arneman44/Modular-Lab-PowerSupply/Docs/page_1.png

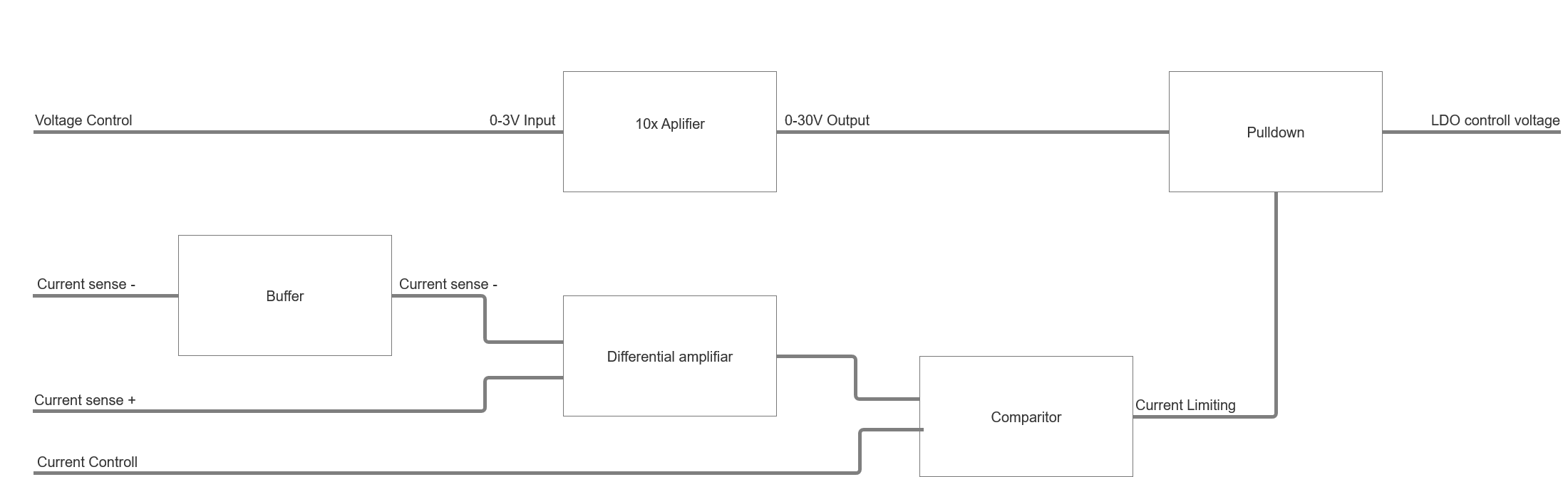
Docs/page_1.png
