arneman44/Modular-Lab-PowerSupply/Docs/power_module.png

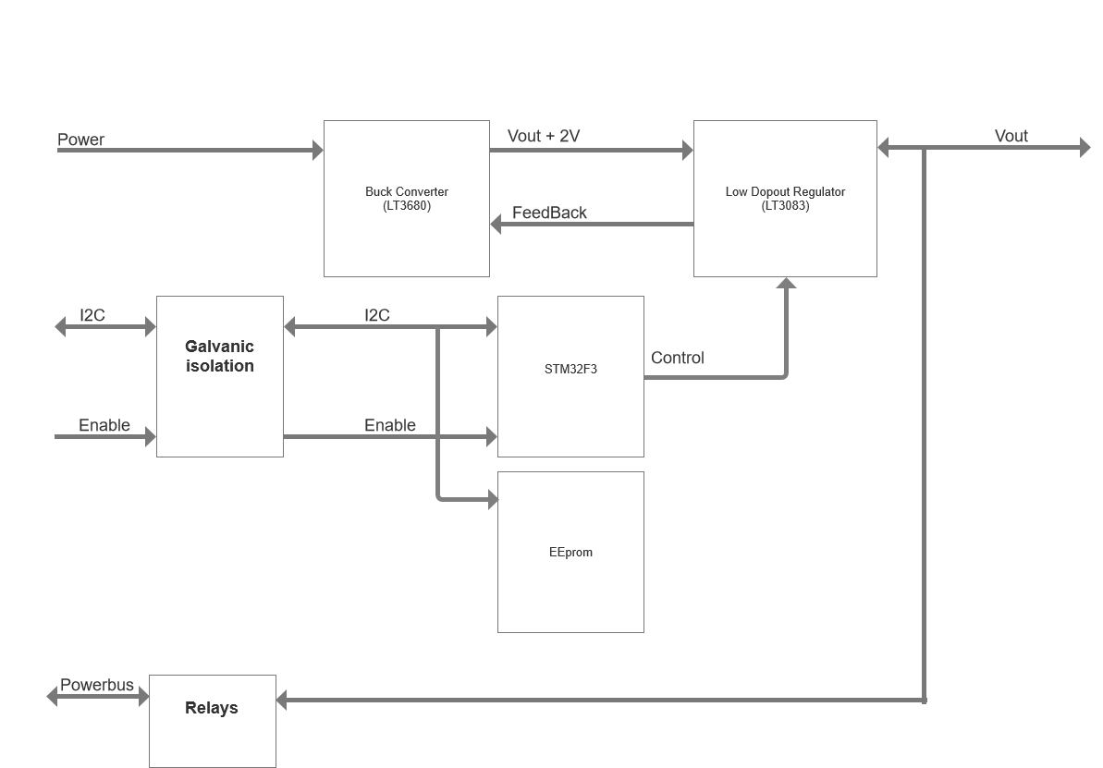
Docs/power_module.png
