arneman44/Modular-Lab-PowerSupply/LCDboard/LCDboard/STM32_LCD/LCD.kicad_sch

## KiCad design LCDboard/LCDboard/STM32_LCD/LCD.kicad_sch (2021-03-07)

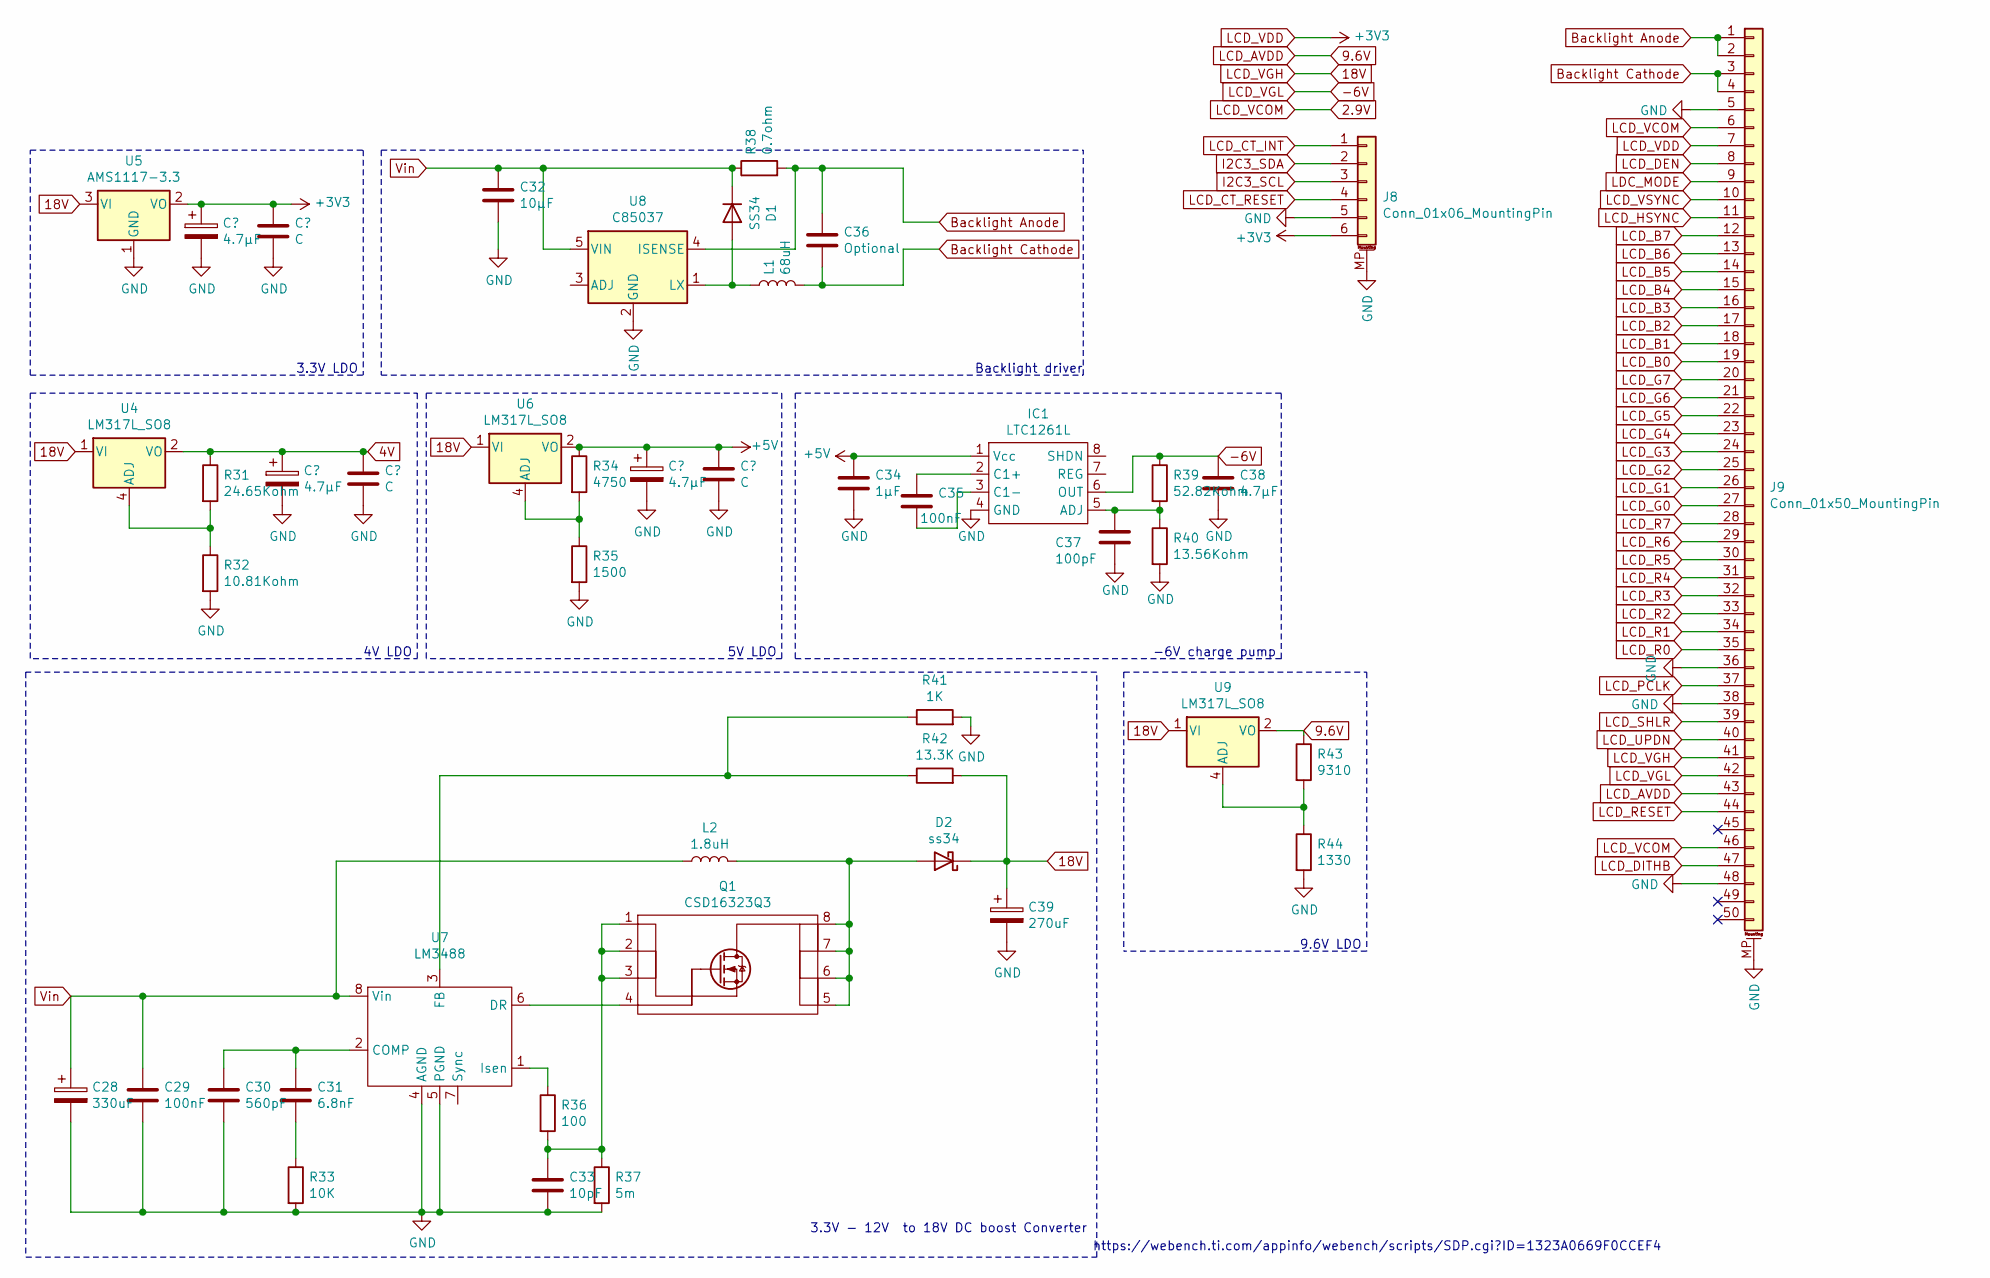
[picture p26: schematic LCD.kicad_sch]

Parts:
C28: 330uF
C29, C35: 100nF
C30: 560pF
C31: 6.8nF
C32: 10µF; C_1206_3216Metric_Pad1.42x1.75mm_HandSolder
C33: 10pF
C34: 1µF
C36: Optional; C_0805_2012Metric_Pad1.15x1.40mm_HandSolder
C37: 100pF
C38: 4.7µF
C39: 270uF
D1: SS34; D_SMA_Handsoldering
D2: ss34
IC1: LTC1261L
J8: Conn_01x06_MountingPin
J9: Conn_01x50_MountingPin
L1: 68uH; L_Bourns-SRN8040_8x8.15mm; Partnr SMNR8040-680MT; LCSC C266439
L2: 1.8uH
Q1: CSD16323Q3; TDSON-8-1
R31: 24.65Kohm
R32: 10.81Kohm
R33: 10K
R34: 4750
R35: 1500
R36: 100
R37: 5m
R38: 0.7ohm; R_1206_3216Metric_Pad1.42x1.75mm_HandSolder
R39: 52.82Kohm
R40: 13.56Kohm
R41: 1K
R42: 13.3K
R43: 9310
R44: 1330
U4, U6, U9: LM317L_SO8; SOIC-8_3.9x4.9mm_P1.27mm
U5: AMS1117-3.3; SOT-223-3_TabPin2
U7: LM3488
U8: C85037; SOT-89-5

Connections:
2.9V: J9.6, J9.46
4V: R31.1, U4.2 (VO), U4.3 (VO), U4.6 (VO), U4.7 (VO)
9.6V: J9.43, R43.1, U9.2 (VO), U9.3 (VO), U9.6 (VO), U9.7 (VO)
18V: C39.1, D2.1 (K), J9.41, R42.2, U4.1 (VI), U5.3 (VI), U6.1 (VI), U9.1 (VI)
+3V3: J8.6, J9.7, U5.2 (VO)
+5V: C34.1, IC1.1 (Vcc), R34.1, U6.2 (VO), U6.3 (VO), U6.6 (VO), U6.7 (VO)
-6V: C38.1, IC1.6 (OUT), J9.42, R39.1
Backlight Anode: C36.1, J9.1, J9.2, R38.2, U8.4 (ISENSE)
Backlight Cathode: C36.2, J9.3, J9.4, L1.2
GND: C28.2, C29.2, C30.2, C32.2, C33.2, C34.2, C37.2, C38.2, C39.2, IC1.4 (GND), J8.5, J8.MP (MountPin), J9.5, J9.36, J9.38, J9.48, J9.MP (MountPin), R32.2, R33.2, R35.2, R37.2, R40.2, R41.2, R44.2, U5.1 (GND), U7.4 (AGND), U7.5 (PGND), U8.2 (GND)
I2C3_SCL: J8.3
I2C3_SDA: J8.2
LCD_B0: J9.19
LCD_B1: J9.18
LCD_B2: J9.17
LCD_B3: J9.16
LCD_B4: J9.15
LCD_B5: J9.14
LCD_B6: J9.13
LCD_B7: J9.12
LCD_CT_INT: J8.1
LCD_CT_RESET: J8.4
LCD_DEN: J9.8
LCD_DITHB: J9.47
LCD_G0: J9.27
LCD_G1: J9.26
LCD_G2: J9.25
LCD_G3: J9.24
LCD_G4: J9.23
LCD_G5: J9.22
LCD_G6: J9.21
LCD_G7: J9.20
LCD_HSYNC: J9.11
LCD_PCLK: J9.37
LCD_R0: J9.35
LCD_R1: J9.34
LCD_R2: J9.33
LCD_R3: J9.32
LCD_R4: J9.31
LCD_R5: J9.30
LCD_R6: J9.29
LCD_R7: J9.28
LCD_RESET: J9.44
LCD_SHLR: J9.39
LCD_UPDN: J9.40
LCD_VSYNC: J9.10
LDC_MODE: J9.9
unnamed: C30.1, C31.1, U7.2 (COMP)
unnamed: C31.2, R33.1
unnamed: C33.1, Q1.1 (S), Q1.2 (S), Q1.3 (S), R36.2, R37.1
unnamed: C35.1, IC1.2 (C1+)
unnamed: C35.2, IC1.3 (C1-)
unnamed: C37.1, IC1.5 (ADJ), R39.2, R40.1
unnamed: D1.2 (A), L1.1, U8.1 (LX)
unnamed: D2.2 (A), L2.2, Q1.5 (D), Q1.6 (D), Q1.7 (D), Q1.8 (D)
unnamed: Q1.2 (S), Q1.3 (S)
unnamed: Q1.4 (G), U7.6 (DR)
unnamed: R31.2, R32.1, U4.4 (ADJ)
unnamed: R34.2, R35.1, U6.4 (ADJ)
unnamed: R36.1, U7.1 (Isen)
unnamed: R41.1, R42.1, U7.3 (FB)
unnamed: R43.2, R44.1, U9.4 (ADJ)
Vin: C28.1, C29.1, C32.1, D1.1 (K), L2.1, R38.1, U7.8 (Vin), U8.5 (VIN)

Notes on the sheet:
3.3V LDO
4V LDO
5V LDO
Backlight driver
3.3V - 12V to 18V DC boost Converter
https://webench.ti.com/appinfo/webench/scripts/SDP.cgi?ID=1323A0669F0CCEF4
-6V charge pump
9.6V LDO
