arneman44/Modular-Lab-PowerSupply/LCDboard/LCDboard/STM32_LCD/STM32_LCD.kicad_sch

## KiCad design LCDboard/LCDboard/STM32_LCD/STM32_LCD.kicad_sch (2021-03-07)

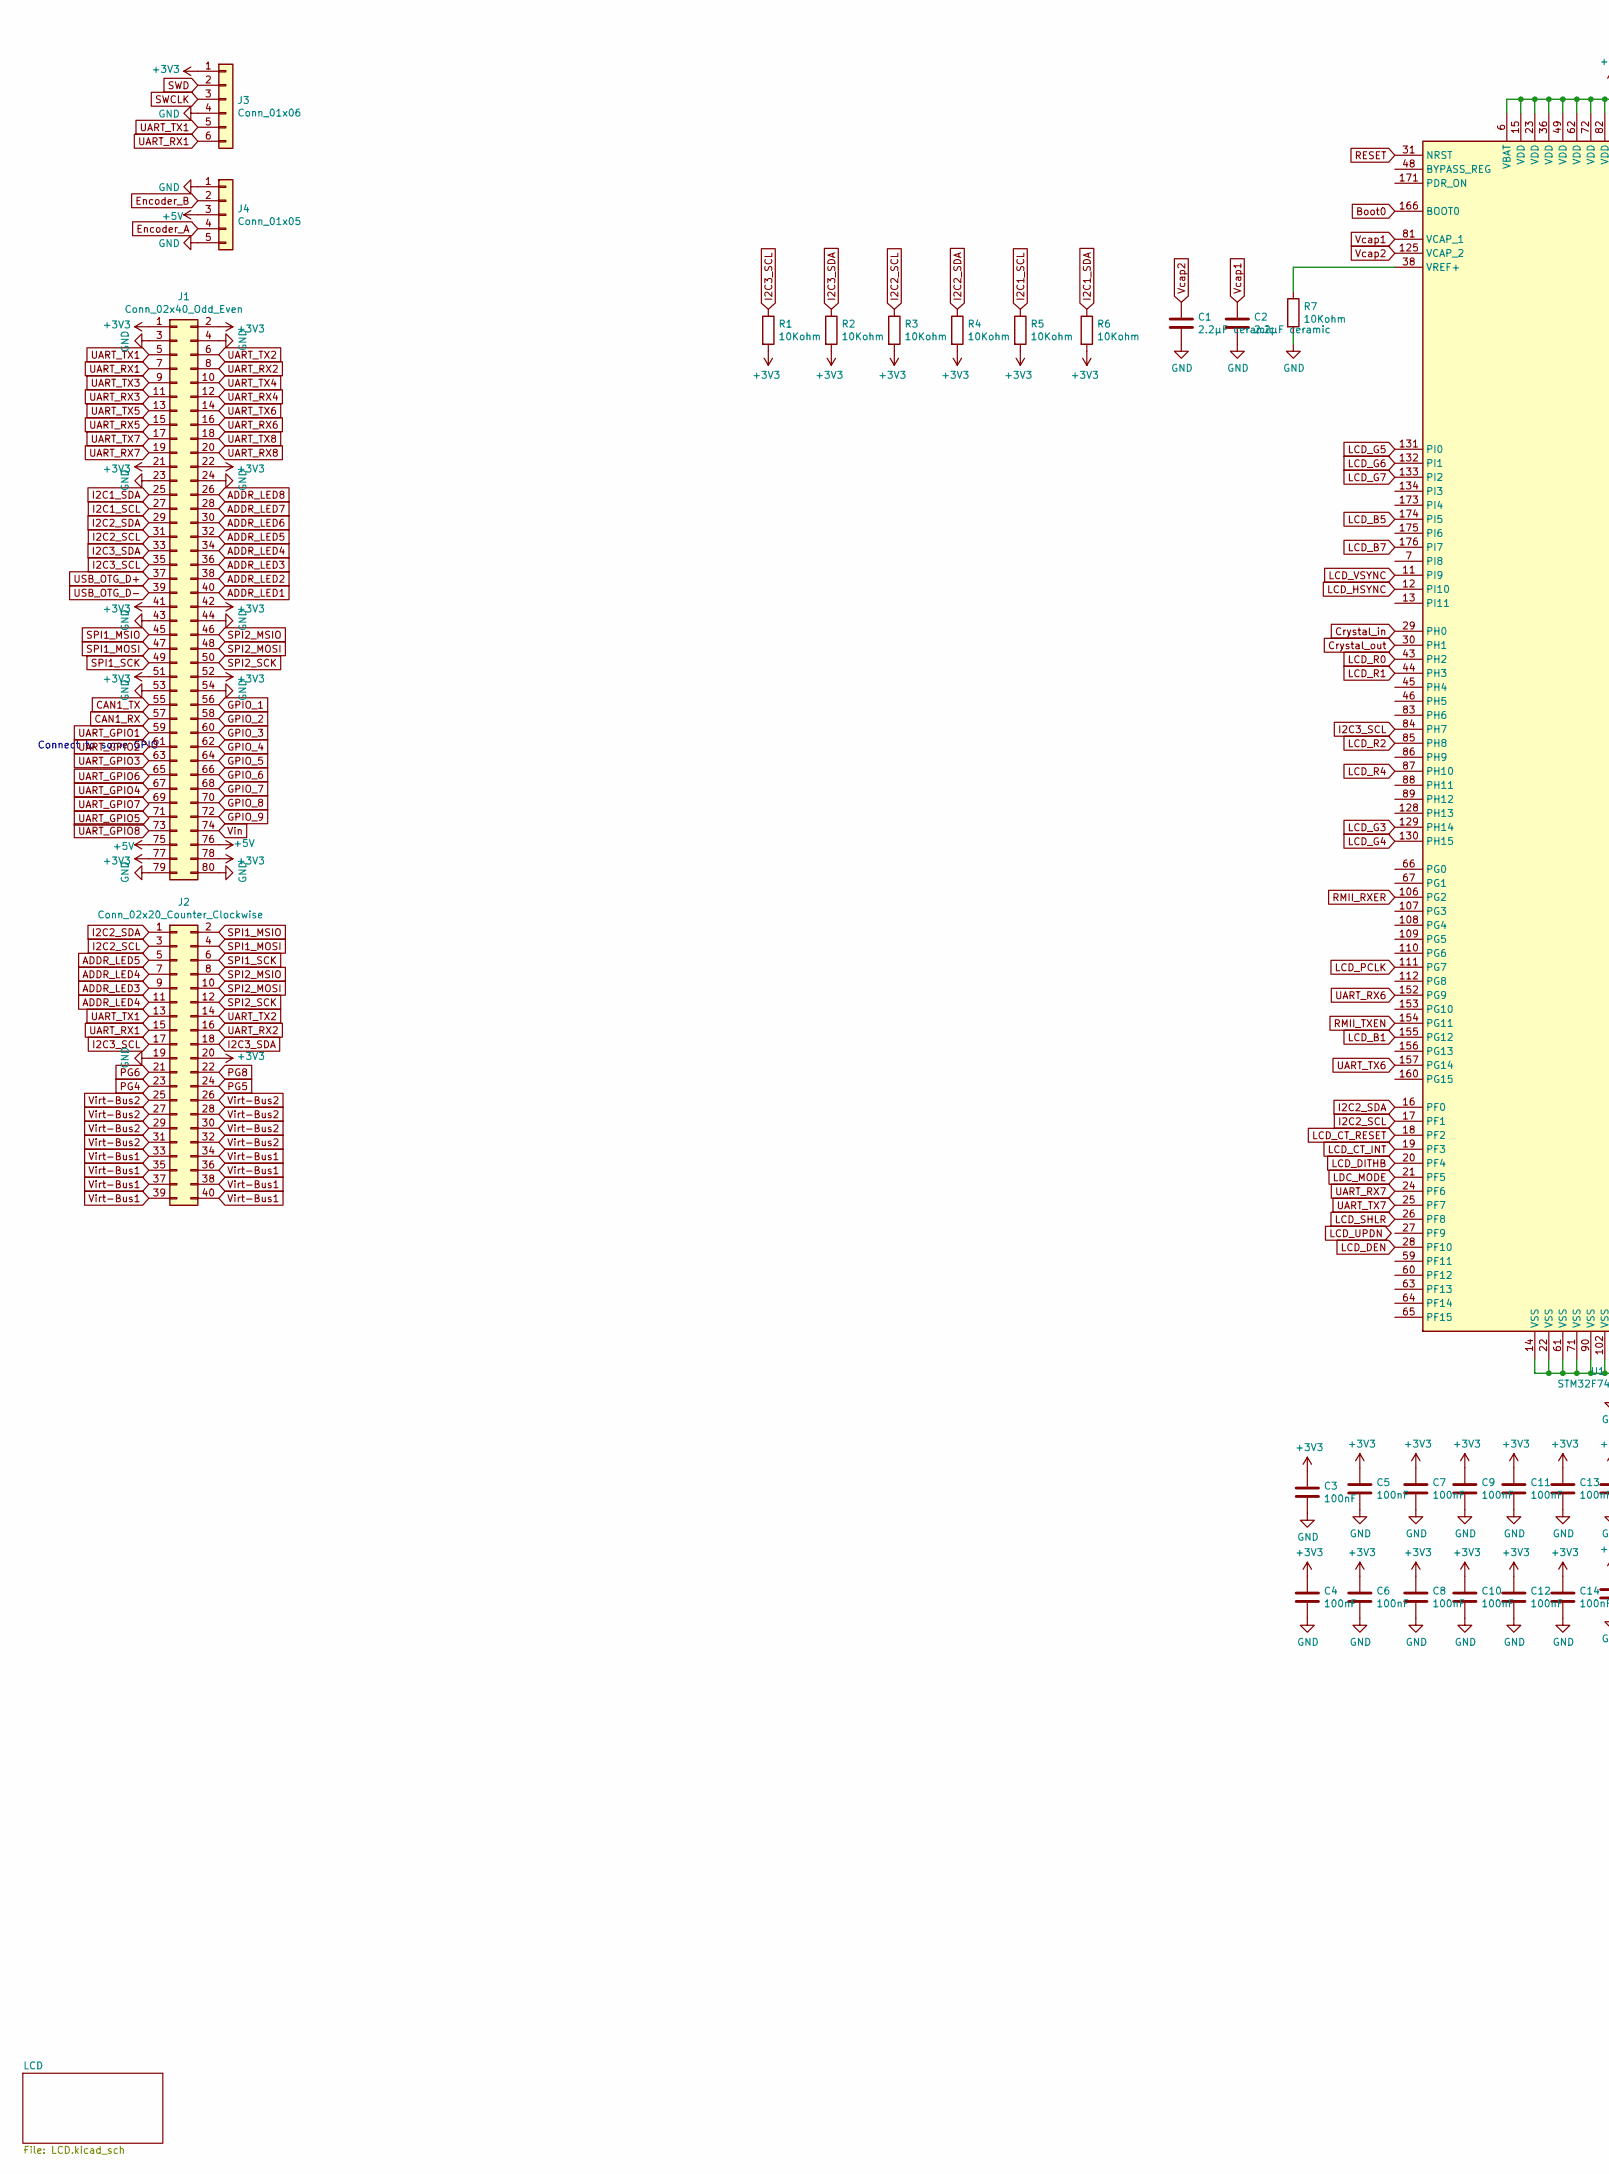
[picture p27: schematic STM32_LCD.kicad_sch, part in row 1, column 1]

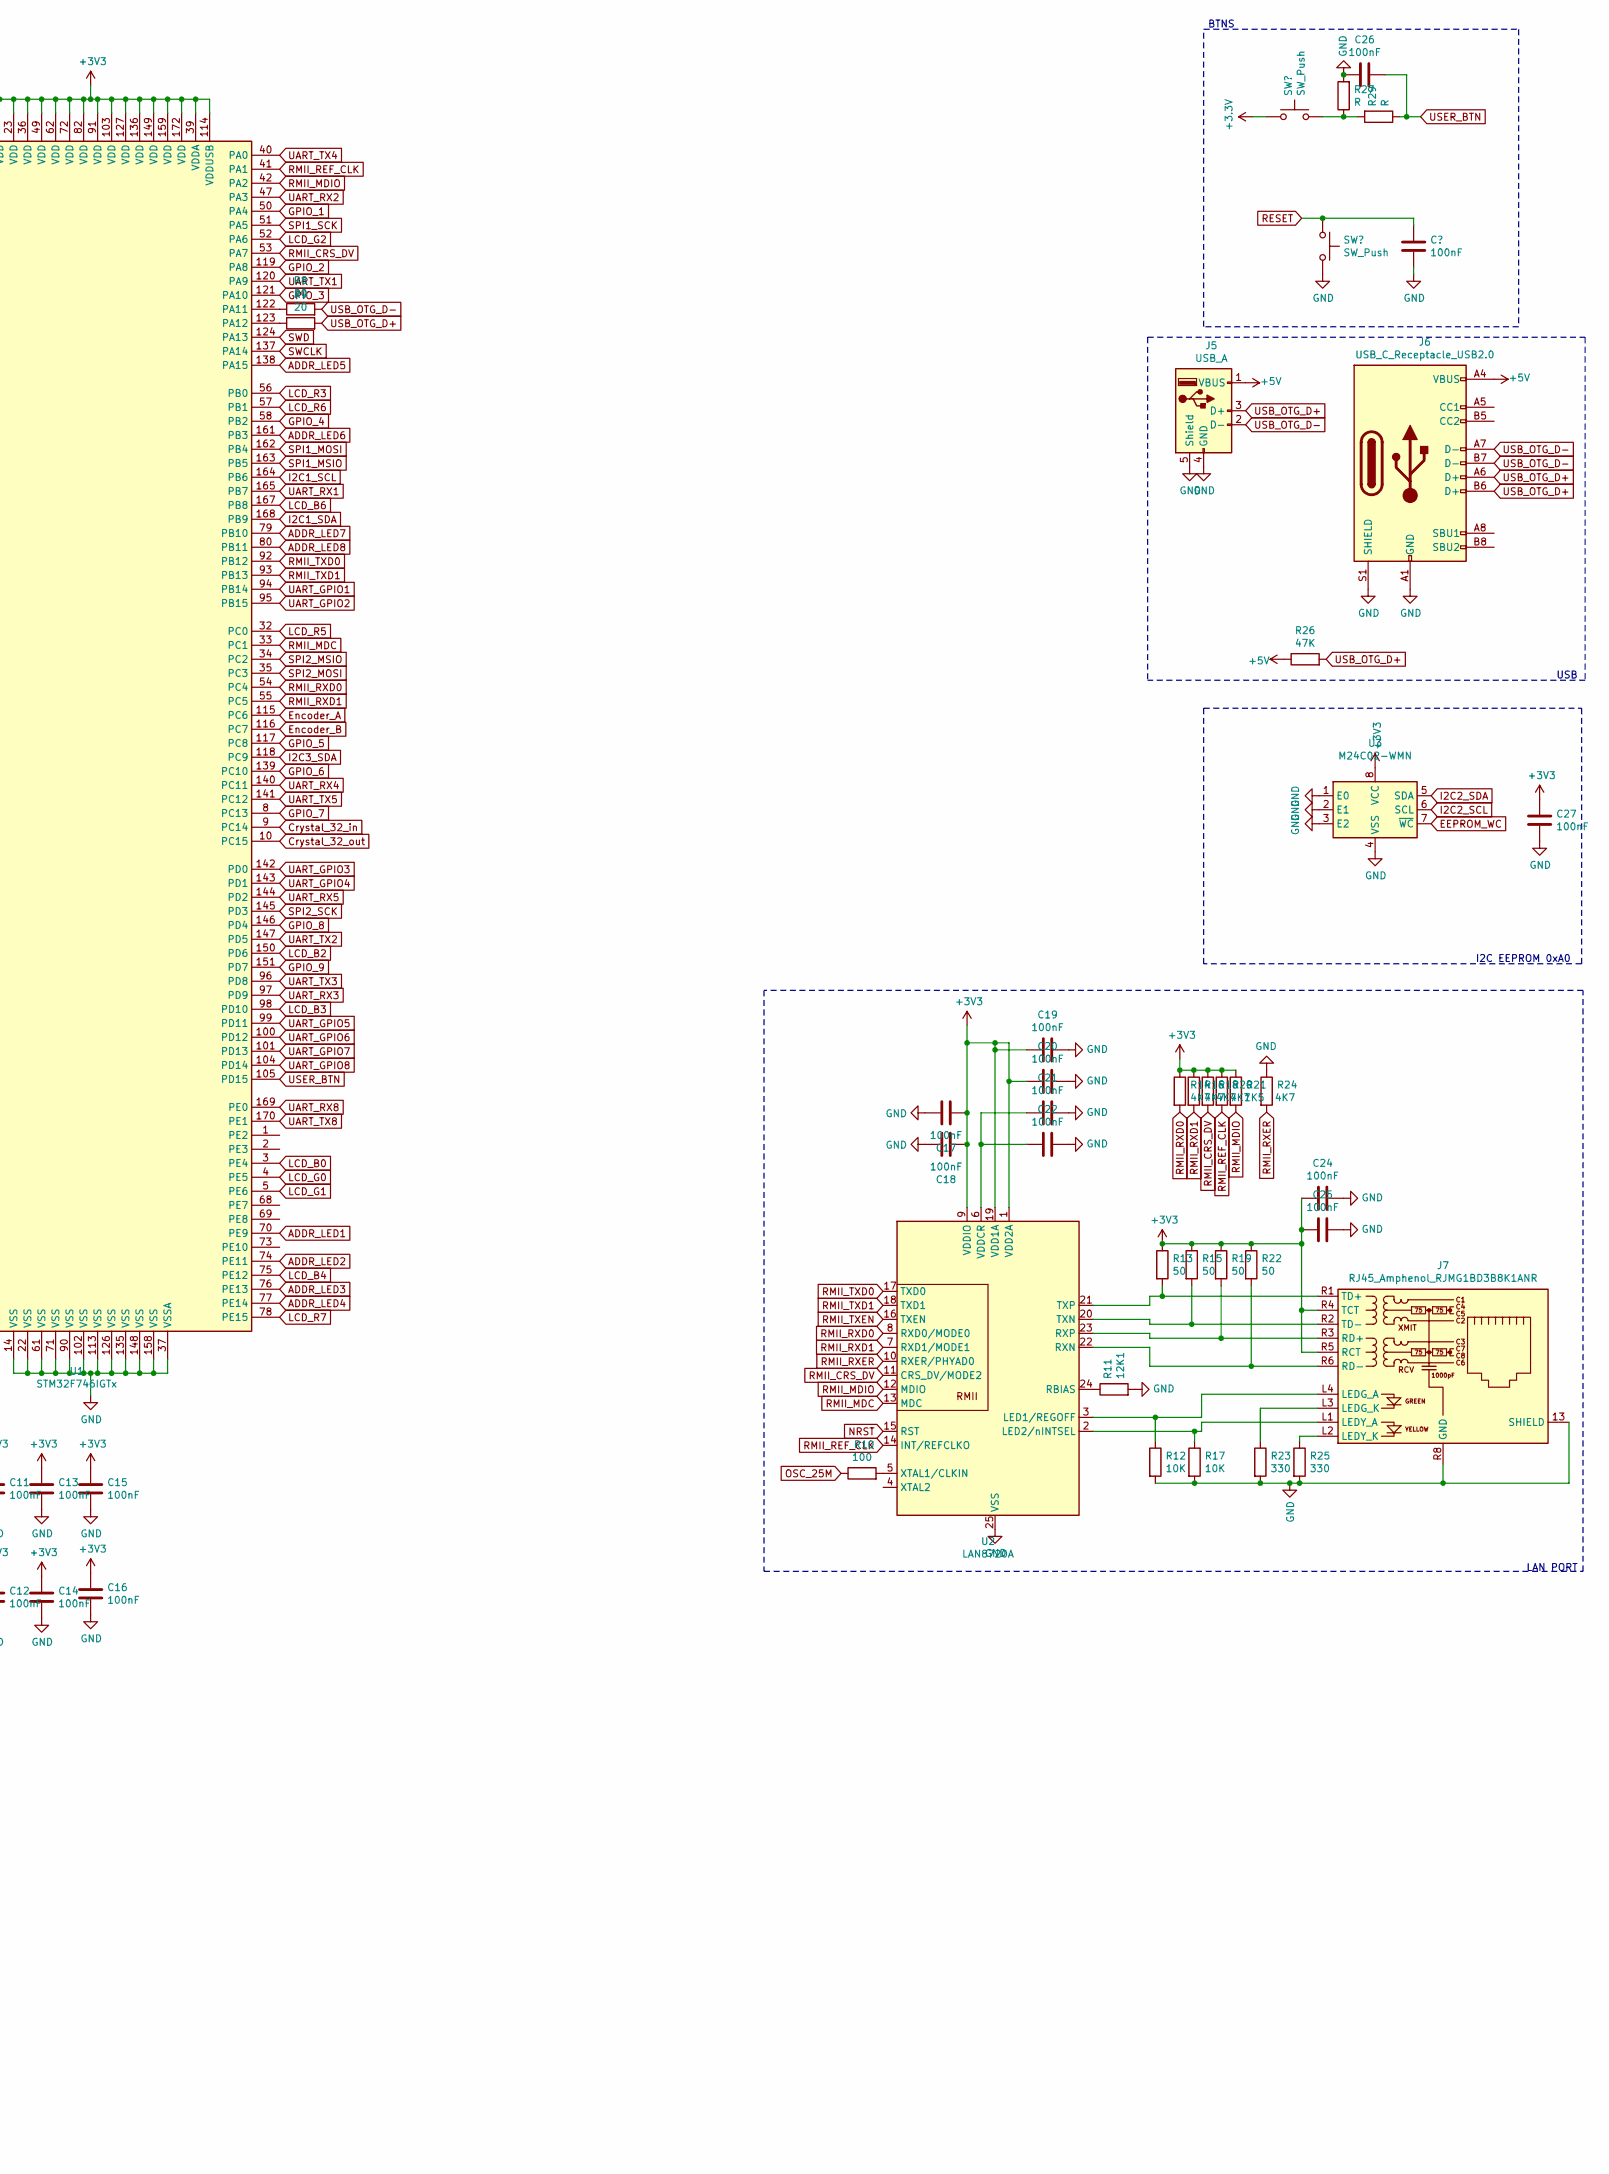
[picture p28: schematic STM32_LCD.kicad_sch, part in row 1, column 2]

Parts:
C1, C2: 2.2µF ceramic
C3, C4, C5, C6, C7, C8, C9, C10, C11, C12, C13, C14, C15, C16, C17, C18, C19, C20, C21, C22, C24, C25, C26, C27: 100nF
J1: Conn_02x40_Odd_Even
J2: Conn_02x20_Counter_Clockwise; PinSocket_2x20_P2.54mm_Vertical
J3: Conn_01x06
J4: Conn_01x05
J5: USB_A
J6: USB_C_Receptacle_USB2.0
J7: RJ45_Amphenol_RJMG1BD3B8K1ANR
R1, R2, R3, R4, R5, R6, R7: 10Kohm
R8, R9: 20
R10: 100
R11: 12K1
R12, R17: 10K
R13, R15, R19, R22: 50
R14, R16, R18, R20, R24: 4K7
R21: 1K5
R23, R25: 330
R26: 47K
R27, R29: R
U1: STM32F746IGTx; LQFP-176_24x24mm_P0.5mm
U2: LAN8720A; QFN-24-1EP_4x4mm_P0.5mm_EP2.6x2.6mm
U3: M24C02-WMN; SOIC-8_3.9x4.9mm_P1.27mm

Connections:
+3V3: C3.1, C4.1, C5.1, C6.1, C7.1, C8.1, C9.1, C10.1, C11.1, C12.1, C13.1, C14.1, C15.1, C16.1, C17.1, C18.1, C19.1, C20.1, C24.1, C25.1, C27.1, J1.1, J1.2, J1.21, J1.22, J1.41, J1.42, J1.51, J1.52, J1.77, J1.78, J2.20, J3.1, J7.R4 (TCT), J7.R5 (RCT), R1.2, R2.2, R3.2, R4.2, R5.2, R6.2, R13.1, R14.1, R15.1, R16.1, R18.1, R19.1, R20.1, R21.1, R22.1, U1.6 (VBAT), U1.15 (VDD), U1.23 (VDD), U1.36 (VDD), U1.39 (VDDA), U1.49 (VDD), U1.62 (VDD), U1.72 (VDD), U1.82 (VDD), U1.91 (VDD), U1.103 (VDD), U1.114 (VDDUSB), U1.127 (VDD), U1.136 (VDD), U1.149 (VDD), U1.159 (VDD), U1.172 (VDD), U2.1 (VDD2A), U2.9 (VDDIO), U2.19 (VDD1A), U3.8 (VCC)
+5V: J1.75, J1.76, J4.3, J5.1 (VBUS), J6.A4 (VBUS), J6.A9 (VBUS), J6.B4 (VBUS), J6.B9 (VBUS), R26.1
ADDR_LED1: J1.40, U1.70 (PE9)
ADDR_LED2: J1.38, U1.74 (PE11)
ADDR_LED3: J1.36, J2.9, U1.76 (PE13)
ADDR_LED4: J1.34, J2.7, J2.11, U1.77 (PE14)
ADDR_LED5: J1.32, J2.5, U1.138 (PA15)
ADDR_LED6: J1.30, U1.161 (PB3)
ADDR_LED7: J1.28, U1.79 (PB10)
ADDR_LED8: J1.26, U1.80 (PB11)
Boot0: U1.166 (BOOT0)
CAN1_RX: J1.57
CAN1_TX: J1.55
Crystal_32_in: U1.9 (PC14)
Crystal_32_out: U1.10 (PC15)
Crystal_in: U1.29 (PH0)
Crystal_out: U1.30 (PH1)
EEPROM_WC: U3.7 (~WC)
Encoder_A: J4.4, U1.115 (PC6)
Encoder_B: J4.2, U1.116 (PC7)
GND: C1.2, C2.2, C3.2, C4.2, C5.2, C6.2, C7.2, C8.2, C9.2, C10.2, C11.2, C12.2, C13.2, C14.2, C15.2, C16.2, C17.2, C18.2, C19.2, C20.2, C21.2, C22.2, C24.2, C25.2, C26.1, C27.2, J1.3, J1.4, J1.23, J1.24, J1.43, J1.44, J1.53, J1.54, J1.79, J1.80, J2.19, J3.4, J4.1, J4.5, J5.4 (GND), J5.5 (Shield), J6.A1 (GND), J6.A12 (GND), J6.B1 (GND), J6.B12 (GND), J6.S1 (SHIELD), J7.13 (SHIELD), J7.R8 (GND), R7.2, R11.2, R12.2, R17.2, R23.2, R24.1, R25.2, R27.2, U1.14 (VSS), U1.22 (VSS), U1.37 (VSSA), U1.61 (VSS), U1.71 (VSS), U1.90 (VSS), U1.102 (VSS), U1.113 (VSS), U1.126 (VSS), U1.135 (VSS), U1.148 (VSS), U1.158 (VSS), U2.25 (VSS), U3.1 (E0), U3.2 (E1), U3.3 (E2), U3.4 (VSS)
GPIO_1: J1.56, U1.50 (PA4)
GPIO_2: J1.58, U1.119 (PA8)
GPIO_3: J1.60, U1.121 (PA10)
GPIO_4: J1.62, U1.58 (PB2)
GPIO_5: J1.64, U1.117 (PC8)
GPIO_6: J1.66, U1.139 (PC10)
GPIO_7: J1.68, U1.8 (PC13)
GPIO_8: J1.70, U1.146 (PD4)
GPIO_9: J1.72, U1.151 (PD7)
I2C1_SCL: J1.27, R5.1, U1.164 (PB6)
I2C1_SDA: J1.25, R6.1, U1.168 (PB9)
I2C2_SCL: J1.31, J2.3, R3.1, U1.17 (PF1), U3.6 (SCL)
I2C2_SDA: J1.29, J2.1, R4.1, U1.16 (PF0), U3.5 (SDA)
I2C3_SCL: J1.35, J2.17, R1.1, U1.84 (PH7)
I2C3_SDA: J1.33, J2.18, R2.1, U1.118 (PC9)
LCD_B0: U1.3 (PE4)
LCD_B1: U1.155 (PG12)
LCD_B2: U1.150 (PD6)
LCD_B3: U1.98 (PD10)
LCD_B4: U1.75 (PE12)
LCD_B5: U1.174 (PI5)
LCD_B6: U1.167 (PB8)
LCD_B7: U1.176 (PI7)
LCD_CT_INT: U1.19 (PF3)
LCD_CT_RESET: U1.18 (PF2)
LCD_DEN: U1.28 (PF10)
LCD_DITHB: U1.20 (PF4)
LCD_G0: U1.4 (PE5)
LCD_G1: U1.5 (PE6)
LCD_G2: U1.52 (PA6)
LCD_G3: U1.129 (PH14)
LCD_G4: U1.130 (PH15)
LCD_G5: U1.131 (PI0)
LCD_G6: U1.132 (PI1)
LCD_G7: U1.133 (PI2)
LCD_HSYNC: U1.12 (PI10)
LCD_PCLK: U1.111 (PG7)
LCD_R0: U1.43 (PH2)
LCD_R1: U1.44 (PH3)
LCD_R2: U1.85 (PH8)
LCD_R3: U1.56 (PB0)
LCD_R4: U1.87 (PH10)
LCD_R5: U1.32 (PC0)
LCD_R6: U1.57 (PB1)
LCD_R7: U1.78 (PE15)
LCD_SHLR: U1.26 (PF8)
LCD_VSYNC: U1.11 (PI9)
LDC_MODE: U1.21 (PF5)
NRST: U2.15 (RST)
unnamed: C21.1, C22.1, U2.6 (VDDCR)
unnamed: J7.L1 (LEDY_A), R17.1, U2.2 (LED2/nINTSEL)
unnamed: J7.L2 (LEDY_K), R25.1
unnamed: J7.L3 (LEDG_K), R23.1
unnamed: J7.L4 (LEDG_A), R12.1, U2.3 (LED1/REGOFF)
unnamed: J7.R1 (TD+), R13.2, U2.21 (TXP)
unnamed: J7.R2 (TD-), R15.2, U2.20 (TXN)
unnamed: J7.R3 (RD+), R19.2, U2.23 (RXP)
unnamed: J7.R6 (RD-), R22.2, U2.22 (RXN)
unnamed: R7.1, U1.38 (VREF+)
unnamed: R8.1, U1.122 (PA11)
unnamed: R9.1, U1.123 (PA12)
unnamed: R10.2, U2.5 (XTAL1/CLKIN)
unnamed: R11.1, U2.24 (RBIAS)
unnamed: R27.1, R29.2
OSC_25M: R10.1
PG4: J2.23
PG5: J2.24
PG6: J2.21
PG8: J2.22
RESET: U1.31 (NRST)
RMII_CRS_DV: R18.2, U1.53 (PA7), U2.11 (CRS_DV/MODE2)
RMII_MDC: U1.33 (PC1), U2.13 (MDC)
RMII_MDIO: R21.2, U1.42 (PA2), U2.12 (MDIO)
RMII_REF_CLK: R20.2, U1.41 (PA1), U2.14 (INT/REFCLKO)
RMII_RXD0: R14.2, U1.54 (PC4), U2.8 (RXD0/MODE0)
RMII_RXD1: R16.2, U1.55 (PC5), U2.7 (RXD1/MODE1)
RMII_RXER: R24.2, U1.106 (PG2), U2.10 (RXER/PHYAD0)
RMII_TXD0: U1.92 (PB12), U2.17 (TXD0)
RMII_TXD1: U1.93 (PB13), U2.18 (TXD1)
RMII_TXEN: U1.154 (PG11), U2.16 (TXEN)
SPI1_MOSI: J1.47, J2.4, U1.162 (PB4)
SPI1_MSIO: J1.45, J2.2, U1.163 (PB5)
SPI1_SCK: J1.49, J2.6, U1.51 (PA5)
SPI2_MOSI: J1.48, J2.10, U1.35 (PC3)
SPI2_MSIO: J1.46, J2.8, U1.34 (PC2)
SPI2_SCK: J1.50, J2.12, U1.145 (PD3)
SWCLK: J3.3, U1.137 (PA14)
SWD: J3.2, U1.124 (PA13)
UART_GPIO1: J1.59, U1.94 (PB14)
UART_GPIO2: J1.61, U1.95 (PB15)
UART_GPIO3: J1.63, U1.142 (PD0)
UART_GPIO4: U1.143 (PD1)
UART_GPIO5: U1.99 (PD11)
UART_GPIO6: U1.100 (PD12)
UART_GPIO7: U1.101 (PD13)
UART_GPIO8: J1.73, U1.104 (PD14)
UART_RX1: J1.7, J2.15, J3.6, U1.165 (PB7)
UART_RX2: J1.8, J2.16, U1.47 (PA3)
UART_RX3: J1.11, U1.97 (PD9)
UART_RX4: J1.12, U1.140 (PC11)
UART_RX5: J1.15, U1.144 (PD2)
UART_RX6: J1.16, U1.152 (PG9)
UART_RX7: J1.19, U1.24 (PF6)
UART_RX8: J1.20, U1.169 (PE0)
UART_TX1: J1.5, J2.13, J3.5, U1.120 (PA9)
UART_TX2: J1.6, J2.14, U1.147 (PD5)
UART_TX3: J1.9, U1.96 (PD8)
UART_TX4: J1.10, U1.40 (PA0)
UART_TX5: J1.13, U1.141 (PC12)
UART_TX6: J1.14, U1.157 (PG14)
UART_TX7: J1.17, U1.25 (PF7)
UART_TX8: J1.18, U1.170 (PE1)
USB_OTG_D+: J1.37, J5.3 (D+), J6.A6 (D+), J6.B6 (D+), R9.2, R26.2
USB_OTG_D-: J1.39, J5.2 (D-), J6.A7 (D-), J6.B7 (D-), R8.2
USER_BTN: C26.2, R29.1, U1.105 (PD15)
Vcap1: C2.1, U1.81 (VCAP_1)
Vcap2: C1.1, U1.125 (VCAP_2)
Vin: J1.74
Virt-Bus1: J2.33, J2.34, J2.35, J2.36, J2.37, J2.38, J2.39, J2.40
Virt-Bus2: J2.25, J2.26, J2.27, J2.28, J2.29, J2.30, J2.31, J2.32

Notes on the sheet:
Connect to some GPIO
BTNS
I2C EEPROM 0xA0
USB
LAN PORT
